NorthCoastModularCollective/Escanaba-Euclidean/hardware/panels/Belle Isle Burst/Belle Isle Burst panel v12 REFERENCE.BMP

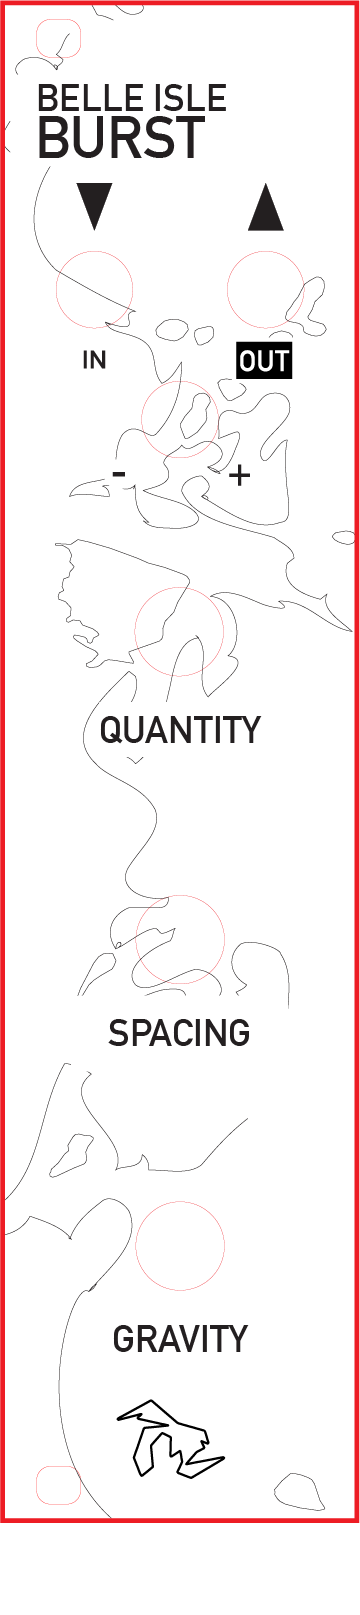
hardware/panels/Belle Isle Burst/Belle Isle Burst panel v12 REFERENCE.BMP
