NorthCoastModularCollective/Escanaba-Euclidean/hardware/panels/Calumet Clock/Calumet Clock panel v12 REFERENCE.BMP

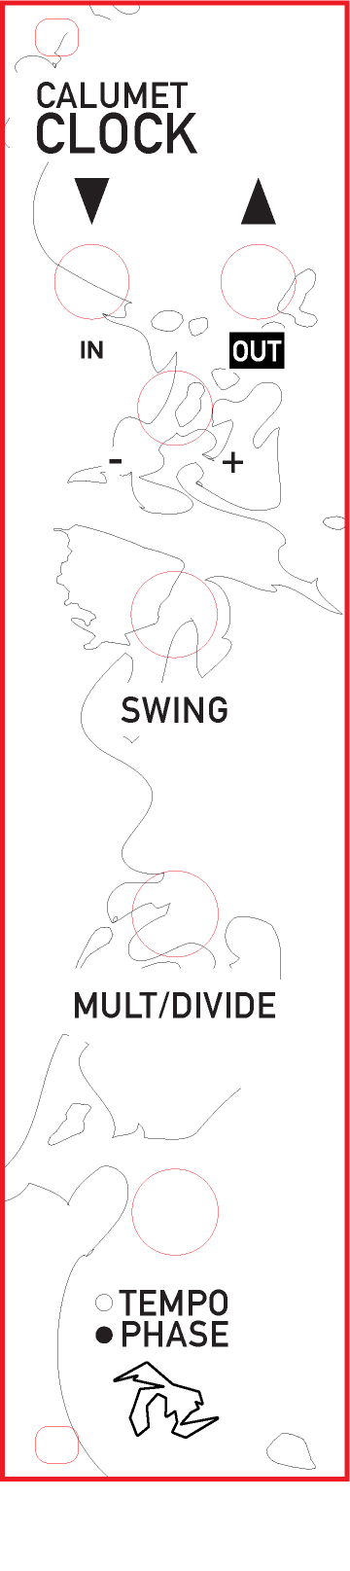
hardware/panels/Calumet Clock/Calumet Clock panel v12 REFERENCE.BMP
