NorthCoastModularCollective/Escanaba-Euclidean/hardware/panels/v12/euclidean panel v12 DrillHoles.BMP

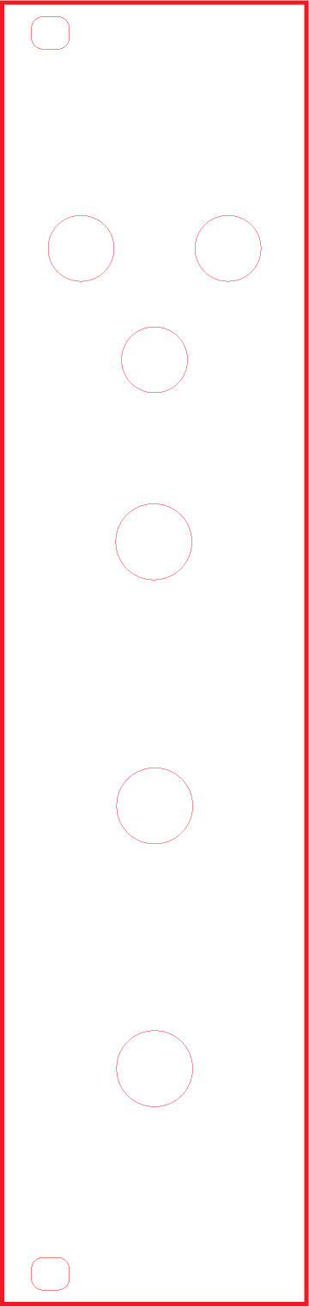
hardware/panels/v12/euclidean panel v12 DrillHoles.BMP
