NorthCoastModularCollective/Escanaba-Euclidean/hardware/panels/v12/euclidean panel v12 DrillHoles.tif

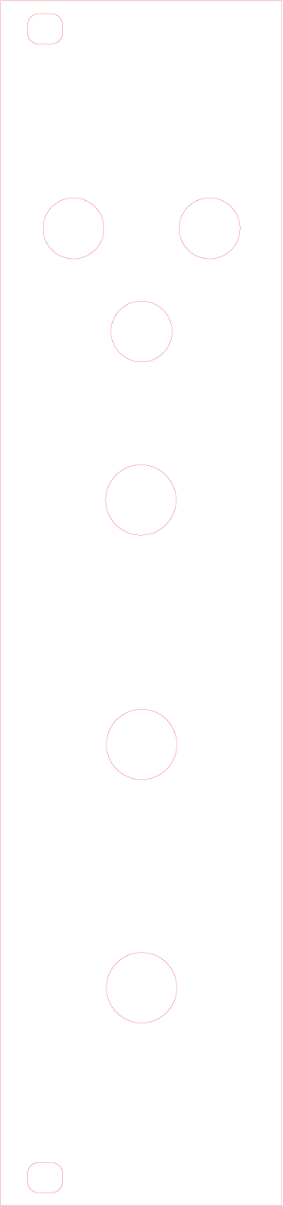
hardware/panels/v12/euclidean panel v12 DrillHoles.tif
