NorthCoastModularCollective/Escanaba-Euclidean/hardware/panels/v12/euclidean panel v12 PanelGraphics.BMP

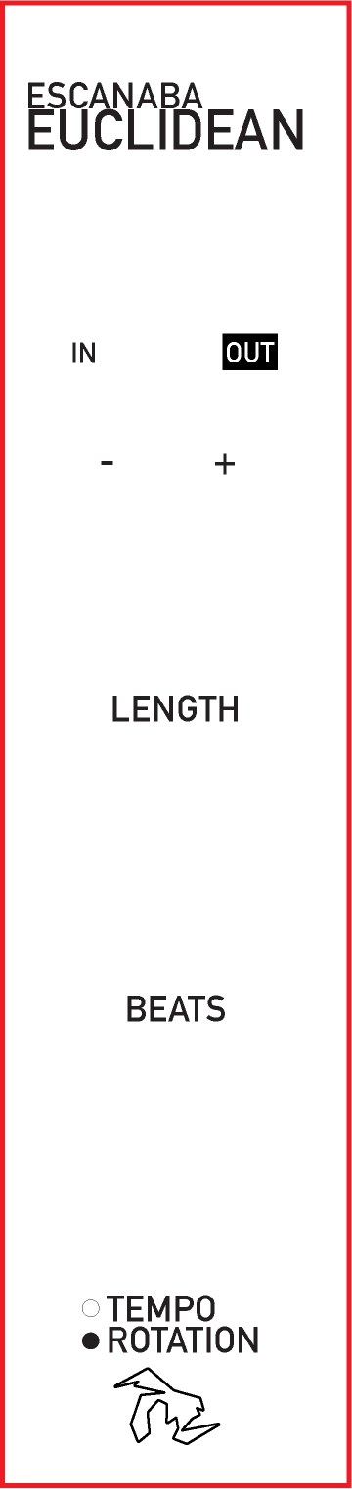
hardware/panels/v12/euclidean panel v12 PanelGraphics.BMP
