NorthCoastModularCollective/Escanaba-Euclidean/hardware/panels/v12/euclidean panel v12 PanelGraphics.tif

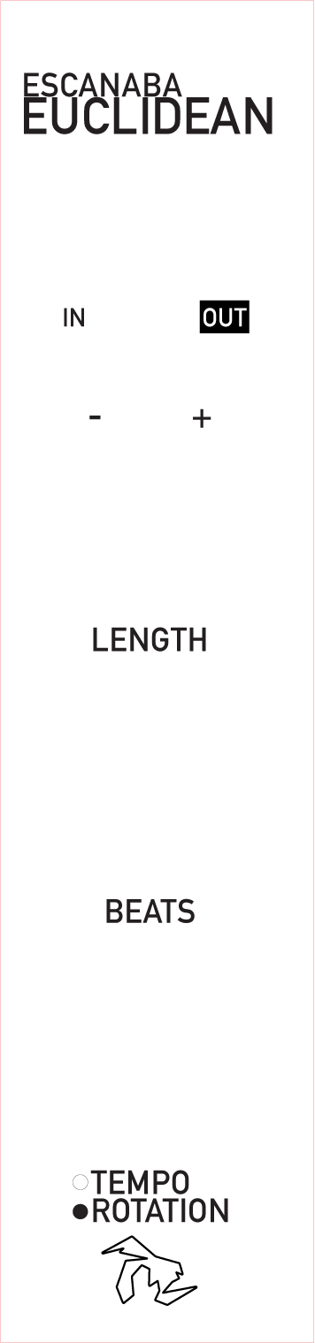
hardware/panels/v12/euclidean panel v12 PanelGraphics.tif
