NorthCoastModularCollective/Escanaba-Euclidean/hardware/panels/v12/euclidean panel v12 REFERENCE.BMP

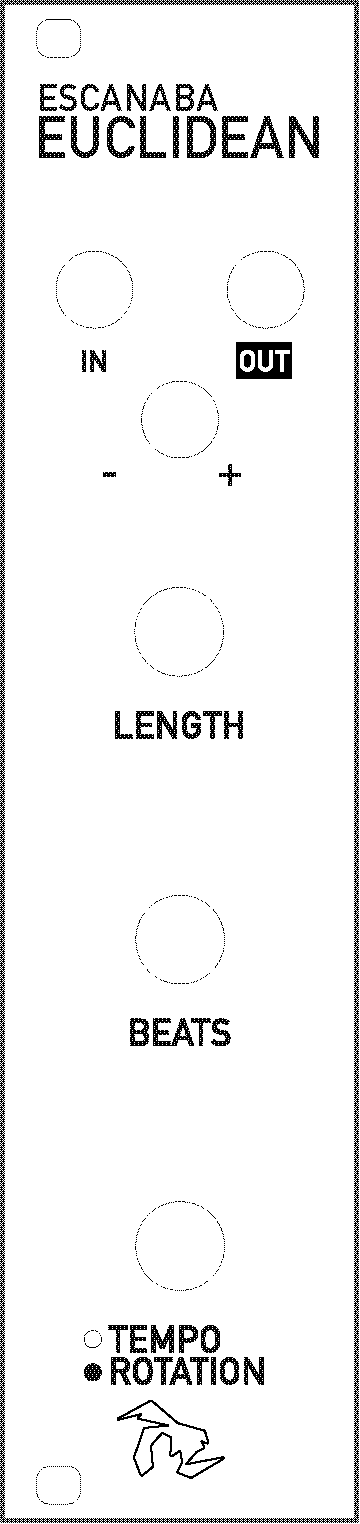
hardware/panels/v12/euclidean panel v12 REFERENCE.BMP
