NorthCoastModularCollective/Escanaba-Euclidean/hardware/panels/v12/euclidean panel v12 TopoLines.BMP

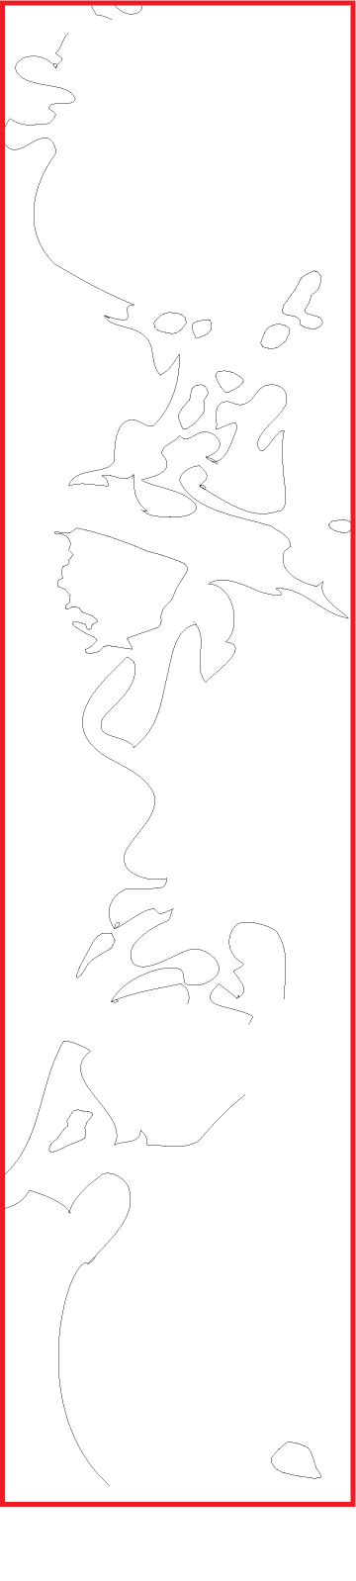
hardware/panels/v12/euclidean panel v12 TopoLines.BMP
