NorthCoastModularCollective/Escanaba-Euclidean/build_guide/IMG_0175.JPG

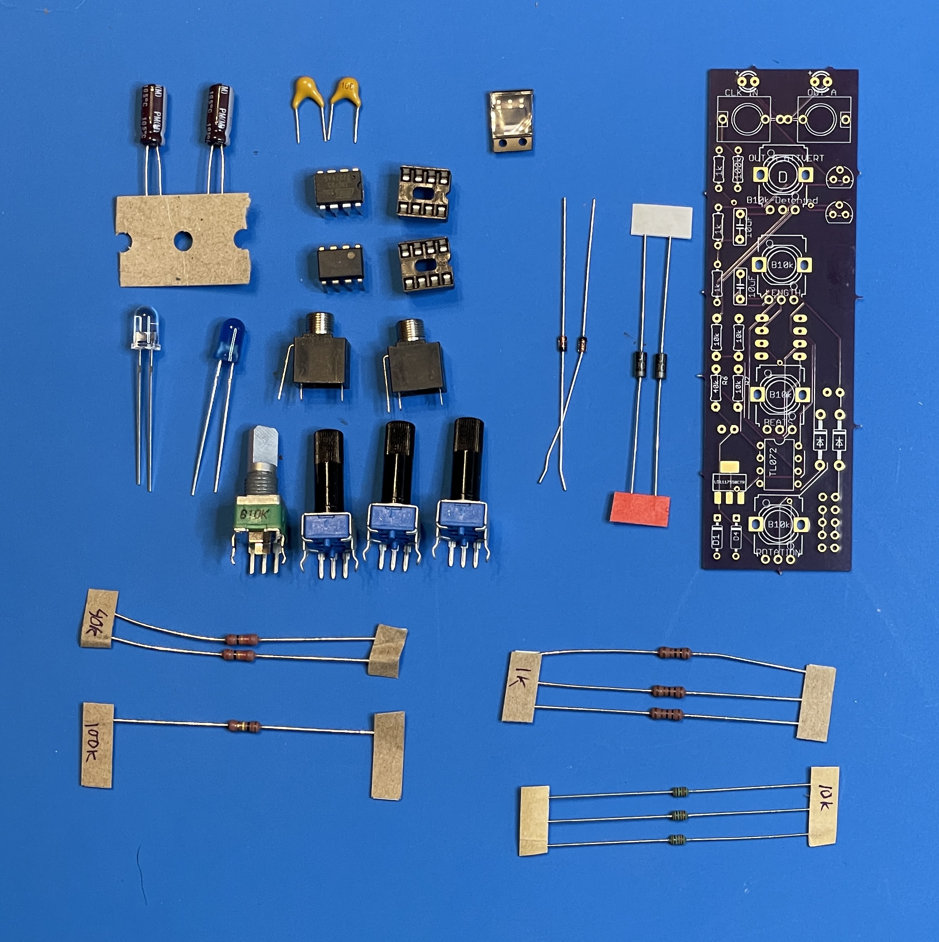
build_guide/IMG_0175.JPG
