NorthCoastModularCollective/Escanaba-Euclidean/build_guide/IMG_0177.JPG

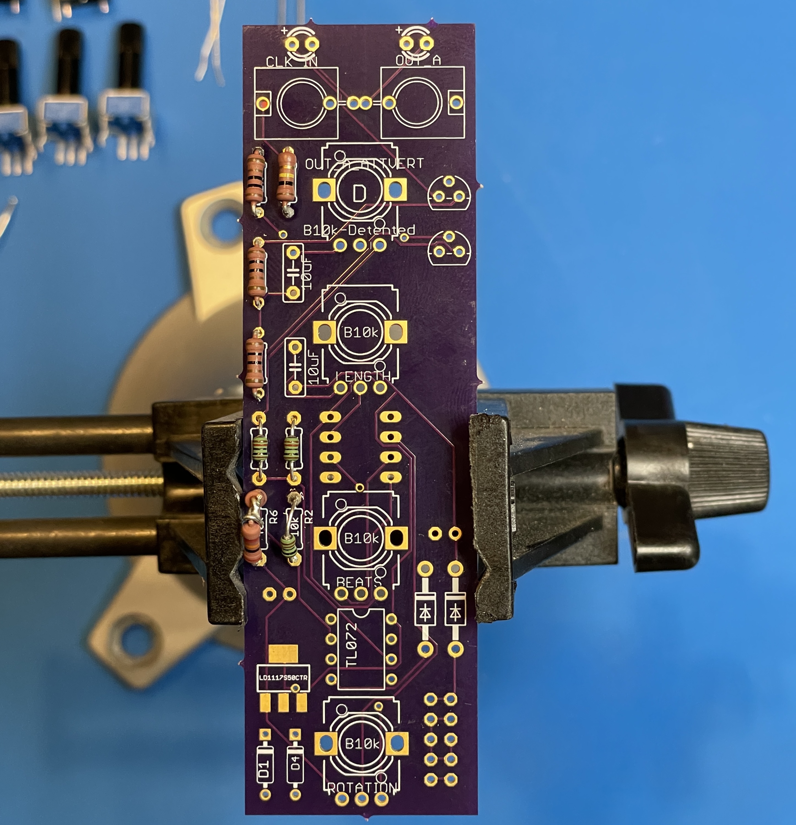
build_guide/IMG_0177.JPG
