NorthCoastModularCollective/Escanaba-Euclidean/build_guide/IMG_0178.JPG

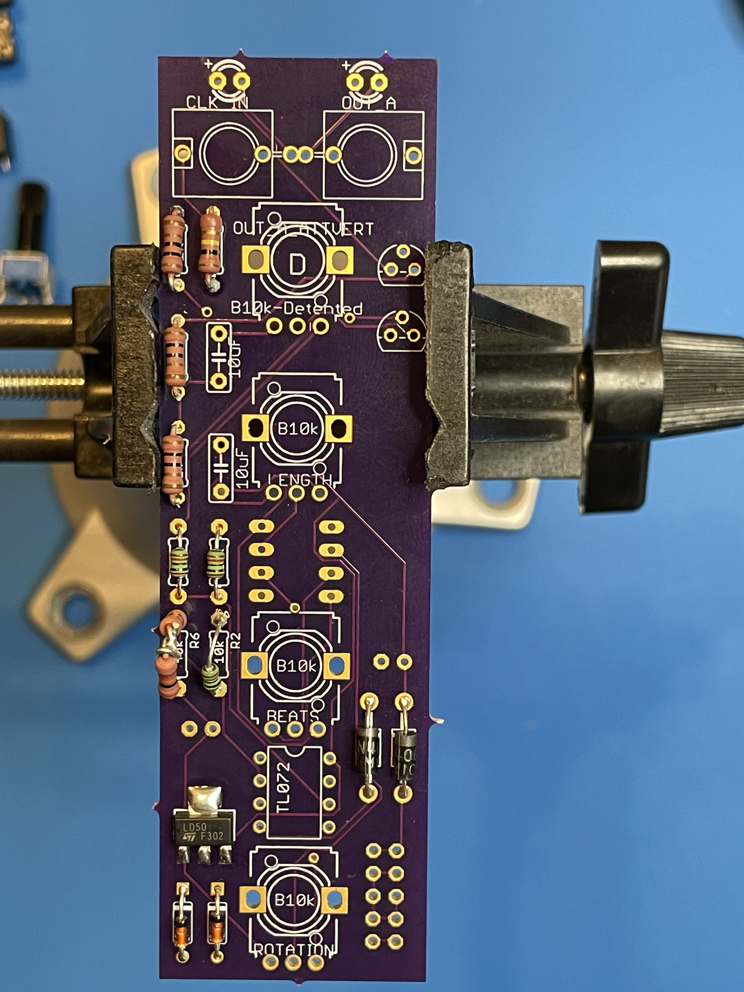
build_guide/IMG_0178.JPG
