NorthCoastModularCollective/Escanaba-Euclidean/build_guide/IMG_0179.JPG

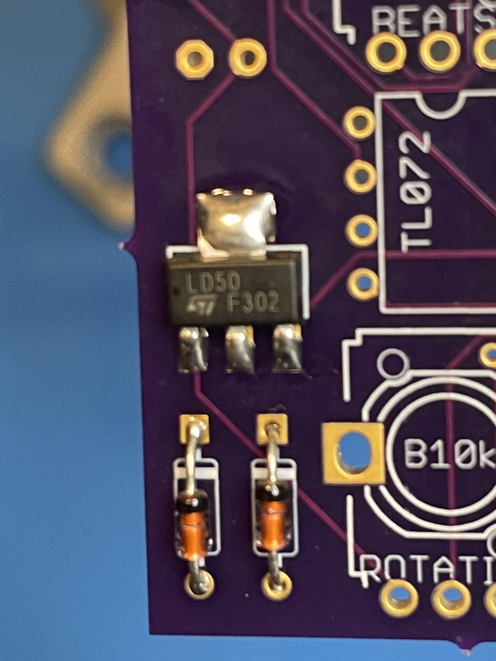
build_guide/IMG_0179.JPG
