NorthCoastModularCollective/Escanaba-Euclidean/build_guide/IMG_0180.JPG

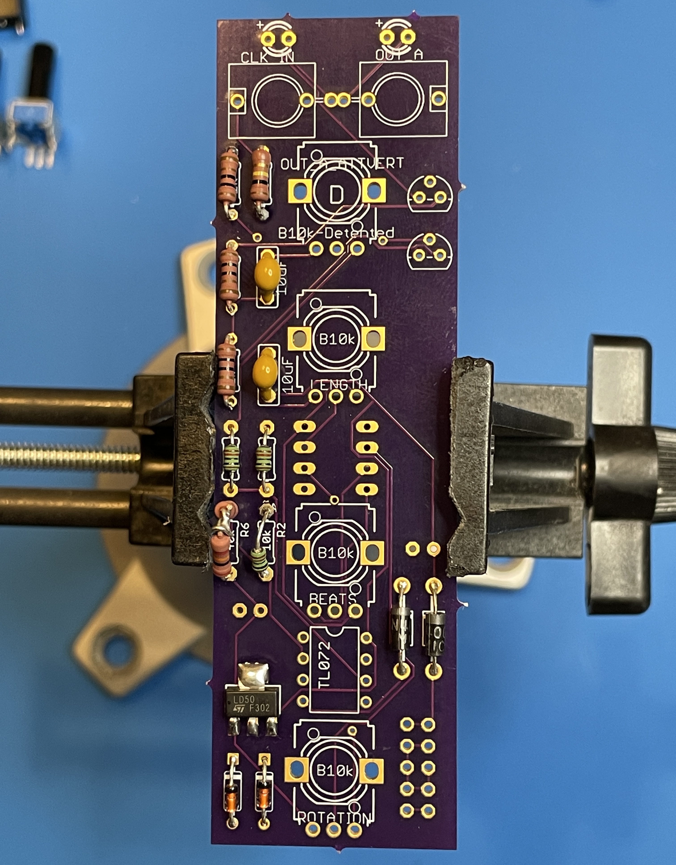
build_guide/IMG_0180.JPG
