NorthCoastModularCollective/Escanaba-Euclidean/build_guide/IMG_0181.JPG

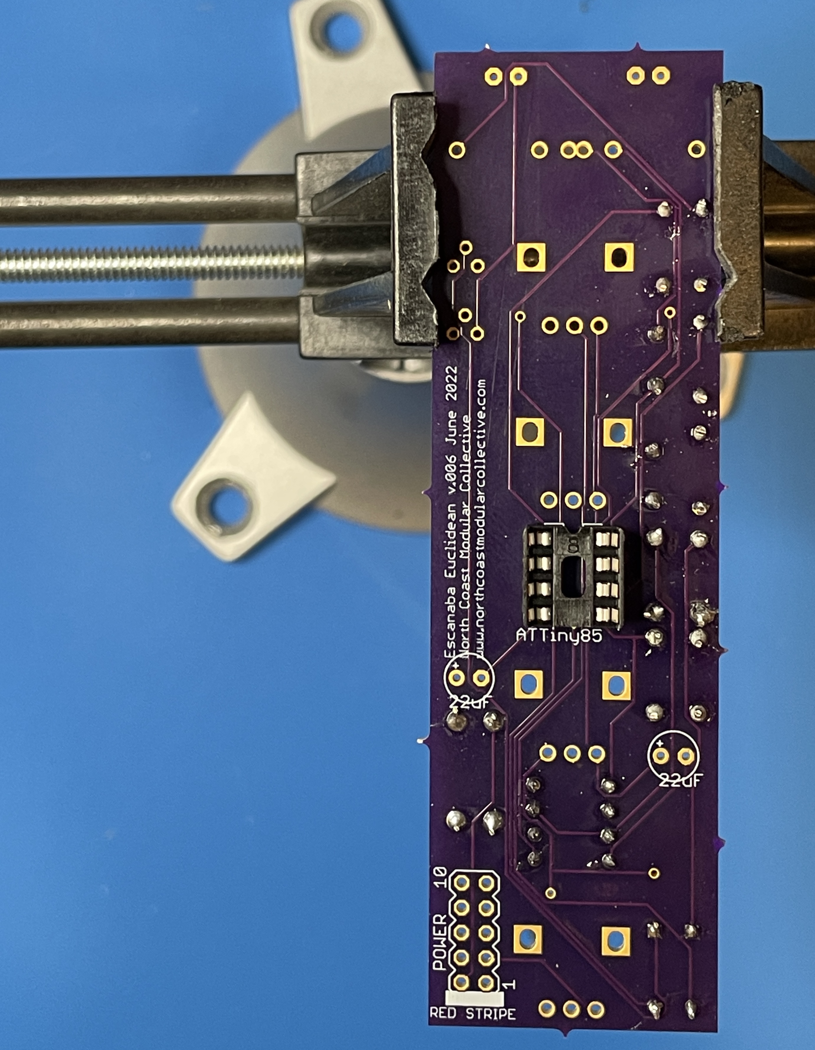
build_guide/IMG_0181.JPG
