NorthCoastModularCollective/Escanaba-Euclidean/build_guide/IMG_0182.JPG

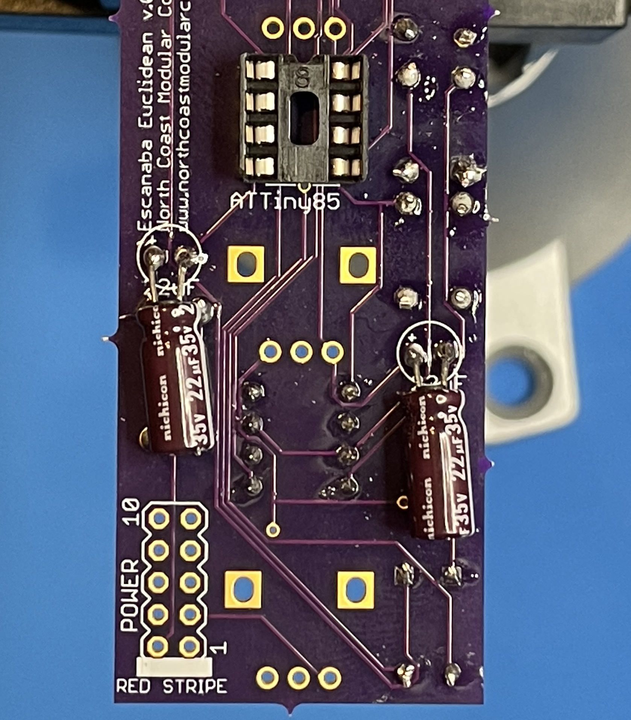
build_guide/IMG_0182.JPG
