NorthCoastModularCollective/Escanaba-Euclidean/build_guide/IMG_0183.JPG

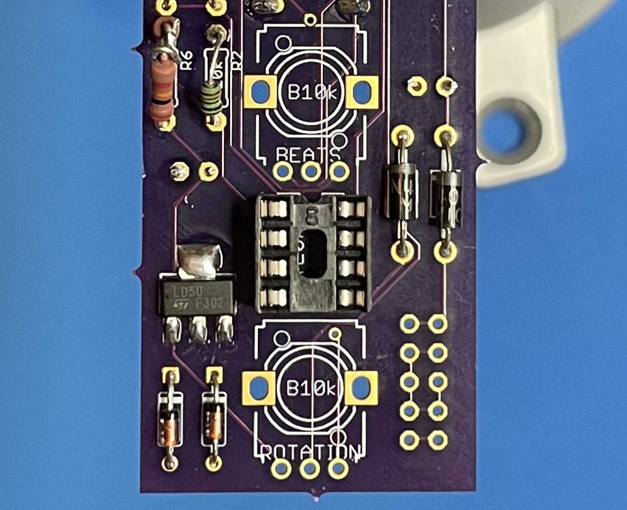
build_guide/IMG_0183.JPG
