NorthCoastModularCollective/Escanaba-Euclidean/build_guide/IMG_0184.JPG

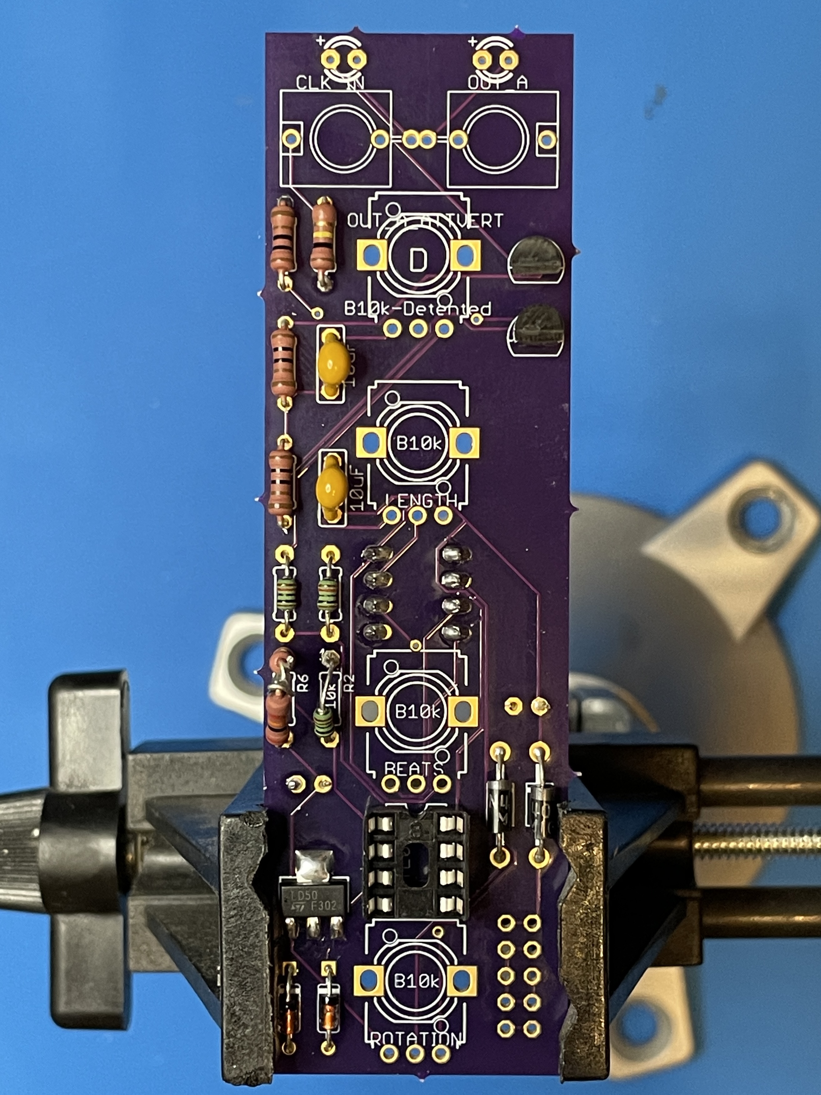
build_guide/IMG_0184.JPG
