NorthCoastModularCollective/Escanaba-Euclidean/build_guide/IMG_0185.JPG

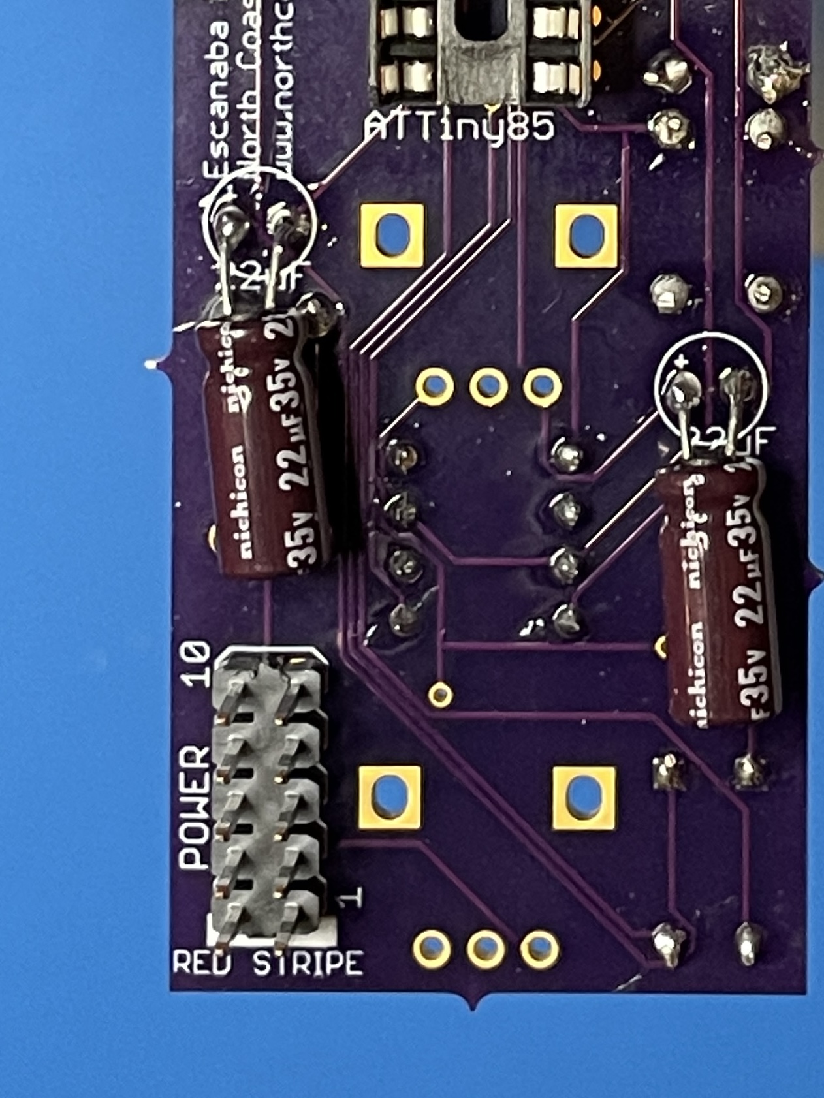
build_guide/IMG_0185.JPG
